drewc830/weather-station/weather-analysis/pressure_change_3h.png

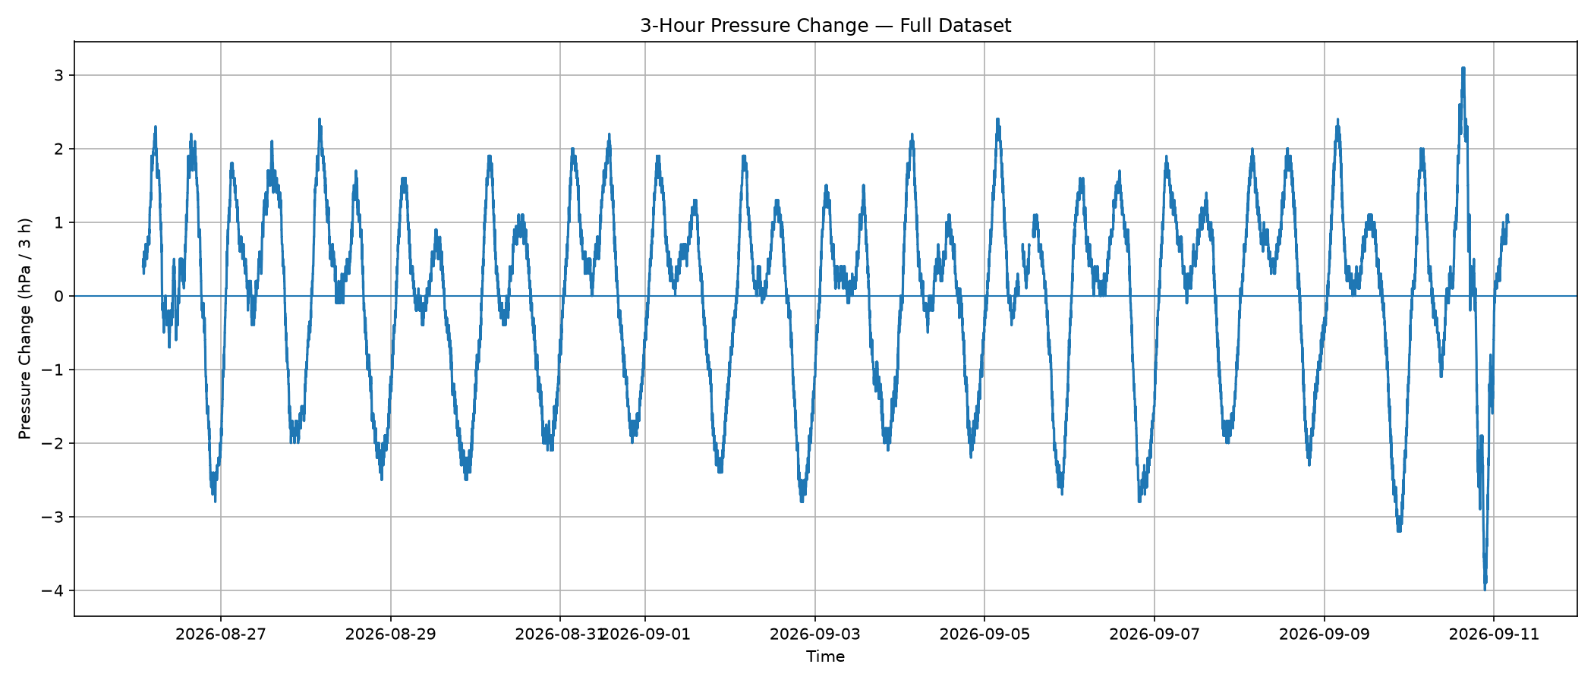
weather-analysis/pressure_change_3h.png
